sucofunk/Beatmakers-Sketchbook-Hardware/solder-guide/images/completeBottomBig.png

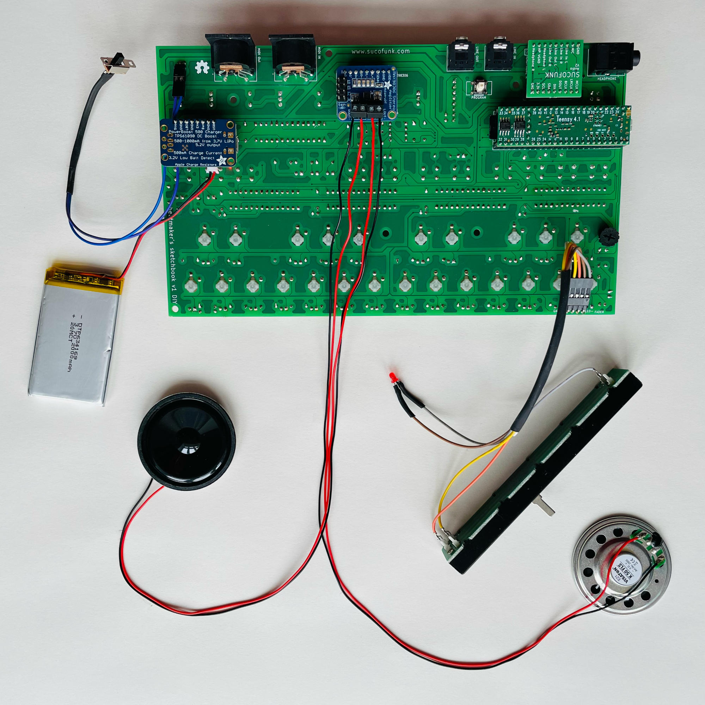
solder-guide/images/completeBottomBig.png
