sucofunk/Beatmakers-Sketchbook-Hardware/solder-guide/images/completeTopBig.png

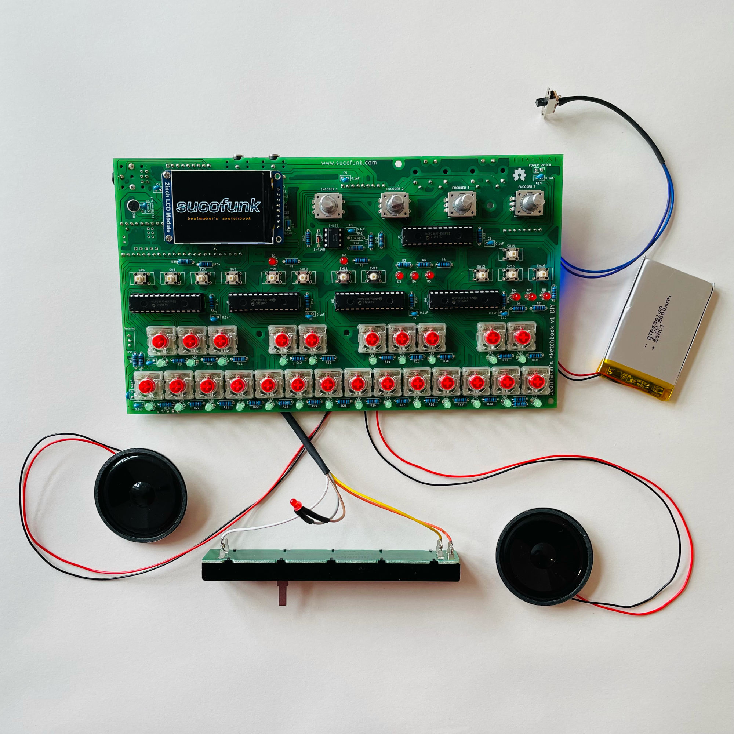
solder-guide/images/completeTopBig.png
